FHanus/MoonClock/MOONCLOCK/symbols.h

/* SYMBOLS.H
 * 
 * Contains all the symbol bitmaps and initializes using them
 * Revision: Filip Hanus, 30/07/2022
 */

// 'A', 48x64px
const unsigned char bitmap_A [] PROGMEM = {
	0x00, 0x00, 0x7f, 0xfe, 0x00, 0x00, 0x00, 0x00, 0x7f, 0xfe, 0x00, 0x00, 0x00, 0x00, 0x7f, 0xff, 
	0x00, 0x00, 0x00, 0x00, 0x7f, 0xff, 0x00, 0x00, 0x00, 0x00, 0xff, 0xff, 0x00, 0x00, 0x00, 0x00, 
	0xff, 0xff, 0x00, 0x00, 0x00, 0x00, 0xff, 0xff, 0x00, 0x00, 0x00, 0x00, 0xff, 0xff, 0x80, 0x00, 
	0x00, 0x01, 0xff, 0xff, 0x80, 0x00, 0x00, 0x01, 0xff, 0xff, 0x80, 0x00, 0x00, 0x01, 0xff, 0xff, 
	0x80, 0x00, 0x00, 0x01, 0xff, 0xff, 0xc0, 0x00, 0x00, 0x03, 0xff, 0x7f, 0xc0, 0x00, 0x00, 0x03, 
	0xff, 0x7f, 0xc0, 0x00, 0x00, 0x03, 0xfe, 0x7f, 0xc0, 0x00, 0x00, 0x03, 0xfe, 0x7f, 0xe0, 0x00, 
	0x00, 0x07, 0xfe, 0x7f, 0xe0, 0x00, 0x00, 0x07, 0xfe, 0x3f, 0xe0, 0x00, 0x00, 0x07, 0xfe, 0x3f, 
	0xe0, 0x00, 0x00, 0x07, 0xfc, 0x3f, 0xf0, 0x00, 0x00, 0x0f, 0xfc, 0x3f, 0xf0, 0x00, 0x00, 0x0f, 
	0xfc, 0x3f, 0xf0, 0x00, 0x00, 0x0f, 0xfc, 0x1f, 0xf0, 0x00, 0x00, 0x0f, 0xfc, 0x1f, 0xf8, 0x00, 
	0x00, 0x1f, 0xf8, 0x1f, 0xf8, 0x00, 0x00, 0x1f, 0xf8, 0x1f, 0xf8, 0x00, 0x00, 0x1f, 0xf8, 0x0f, 
	0xf8, 0x00, 0x00, 0x1f, 0xf8, 0x0f, 0xfc, 0x00, 0x00, 0x1f, 0xf0, 0x0f, 0xfc, 0x00, 0x00, 0x3f, 
	0xf0, 0x0f, 0xfc, 0x00, 0x00, 0x3f, 0xf0, 0x0f, 0xfc, 0x00, 0x00, 0x3f, 0xf0, 0x07, 0xfe, 0x00, 
	0x00, 0x3f, 0xf0, 0x07, 0xfe, 0x00, 0x00, 0x7f, 0xe0, 0x07, 0xfe, 0x00, 0x00, 0x7f, 0xe0, 0x07, 
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
	0x0f, 0xfc, 0x00, 0x00, 0x1f, 0xf8, 0x0f, 0xfc, 0x00, 0x00, 0x1f, 0xf8, 0x0f, 0xfc, 0x00, 0x00, 
	0x1f, 0xf8, 0x0f, 0xfc, 0x00, 0x00, 0x1f, 0xf8, 0x0f, 0xfc, 0x00, 0x00, 0x1f, 0xf8, 0x0f, 0xfc, 
	0x00, 0x00, 0x1f, 0xf8, 0x0f, 0xfc, 0x00, 0x00, 0x1f, 0xf8, 0x0f, 0xfc, 0x00, 0x00, 0x1f, 0xf8
};
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
